BrentSeidel/Arduino-Sensor-Network/Schematics/Basic Responder.kicad_sch

## KiCad design Schematics/Basic Responder.kicad_sch (2023-06-15)

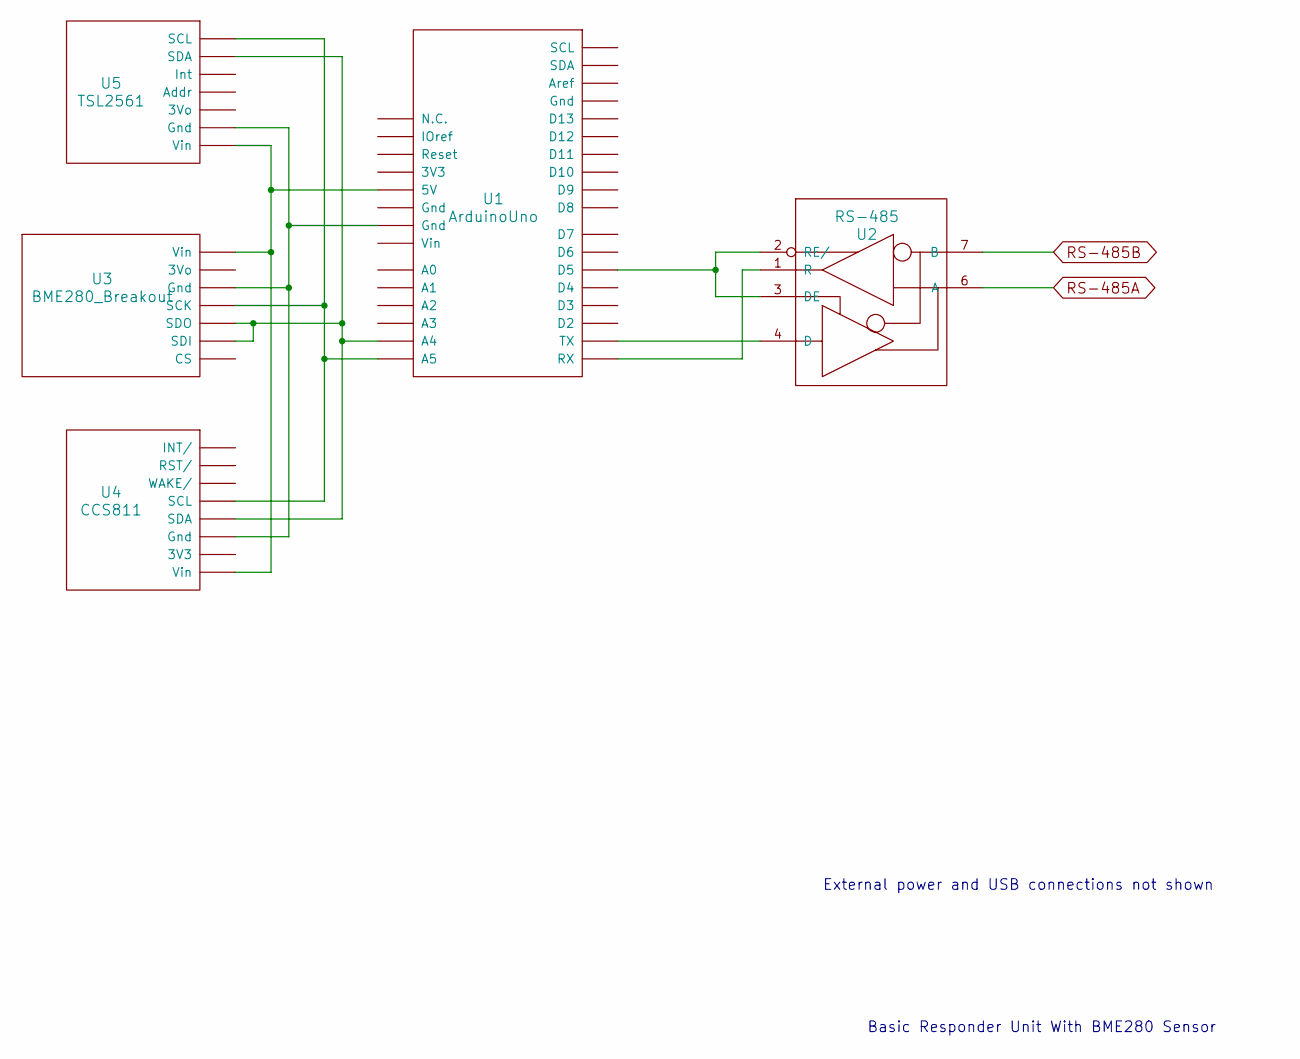
[picture p12: schematic Basic Responder.kicad_sch]

Parts:
U1: ArduinoUno
U2: RS-485
U3: BME280_Breakout
U4: CCS811
U5: TSL2561

Connections:
unnamed: U1.~, U2.1 (R), U2.2 (RE/), U2.3 (DE), U2.4 (D), U3.~, U4.~, U5.~
RS-485A: U2.6 (A)
RS-485B: U2.7 (B)

Notes on the sheet:
External power and USB connections not shown
Basic Responder Unit With BME280 Sensor
