BrentSeidel/Arduino-Sensor-Network/Schematics/Controller.kicad_sch

## KiCad design Schematics/Controller.kicad_sch (2023-06-15)

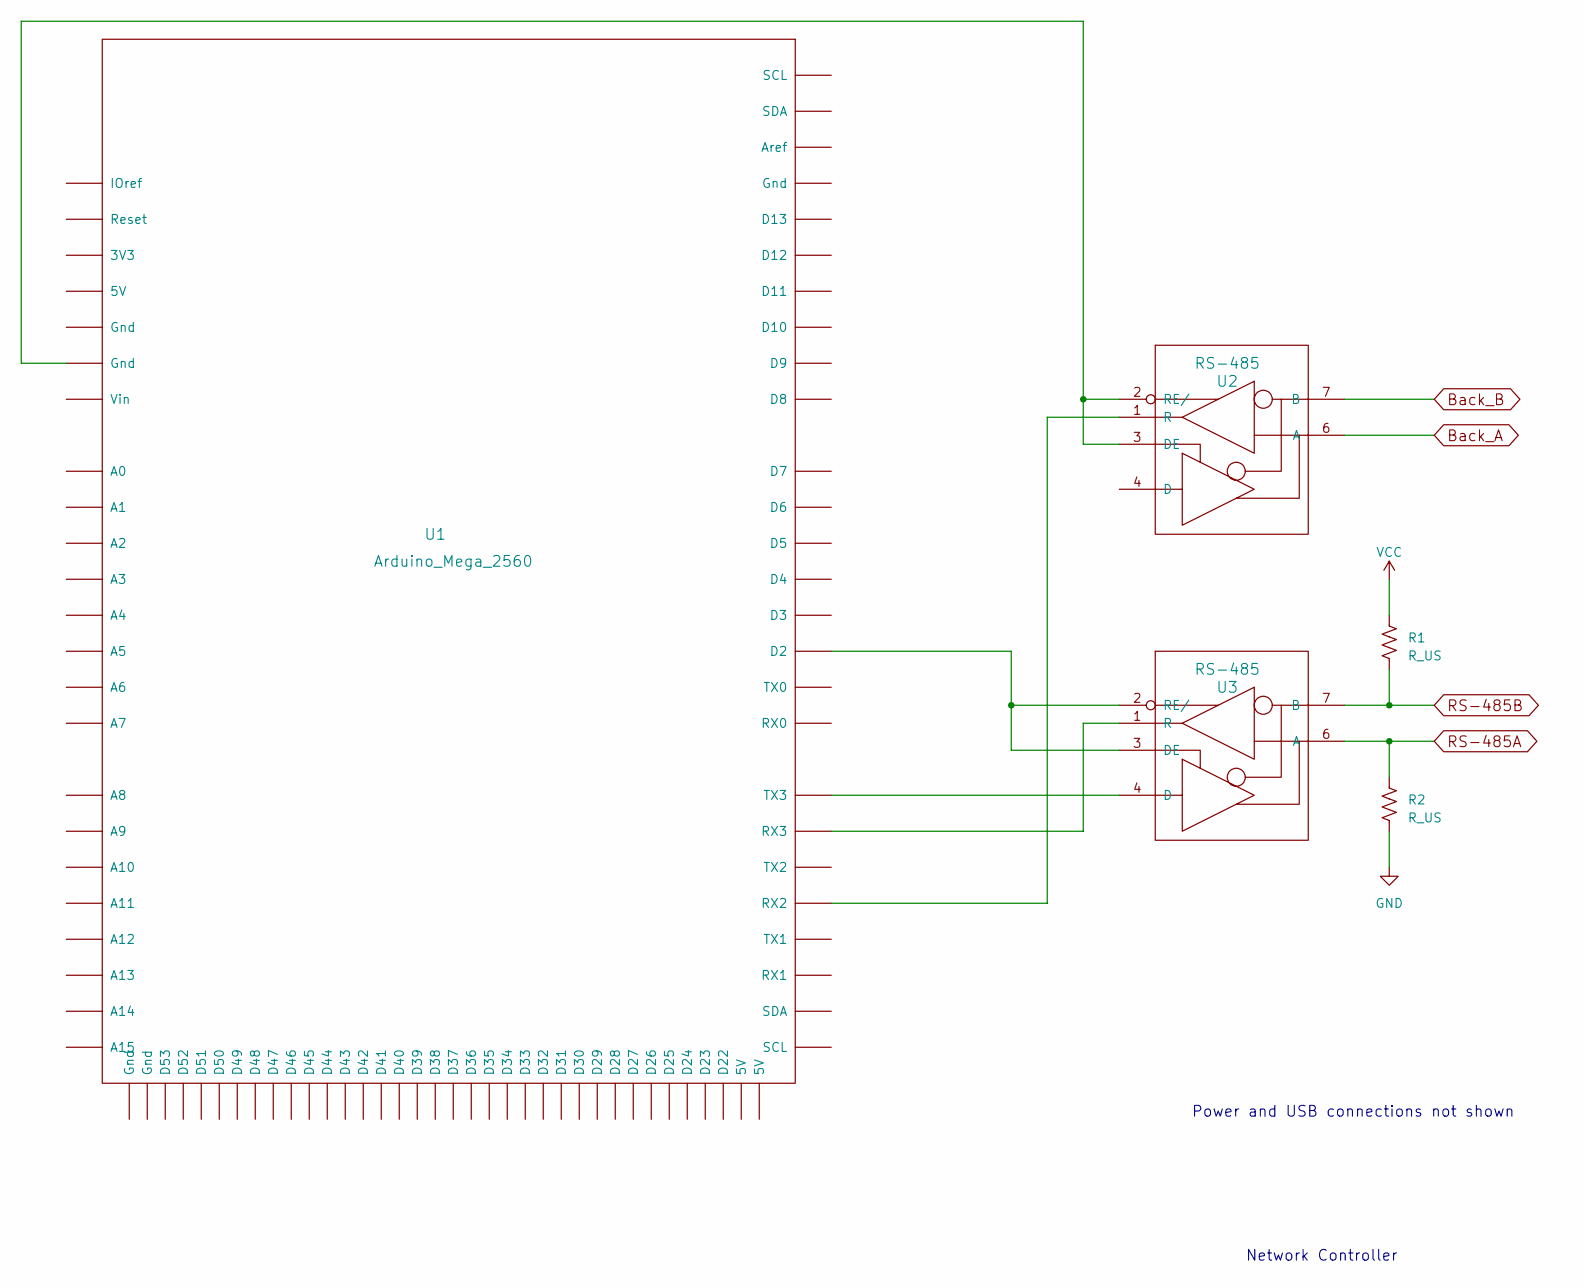
[picture p13: schematic Controller.kicad_sch]

Parts:
R1, R2: R_US
U1: Arduino_Mega_2560
U2, U3: RS-485

Connections:
Back_A: U2.6 (A)
Back_B: U2.7 (B)
GND: R2.2
unnamed: U1.~, U2.1 (R), U2.2 (RE/), U2.3 (DE), U3.1 (R), U3.2 (RE/), U3.3 (DE), U3.4 (D)
RS-485A: R2.1, U3.6 (A)
RS-485B: R1.2, U3.7 (B)
VCC: R1.1

Notes on the sheet:
Power and USB connections not shown
Network Controller
