BrentSeidel/Arduino-Sensor-Network/Schematics/Web Gateway.kicad_sch

## KiCad design Schematics/Web Gateway.kicad_sch (2023-06-15)

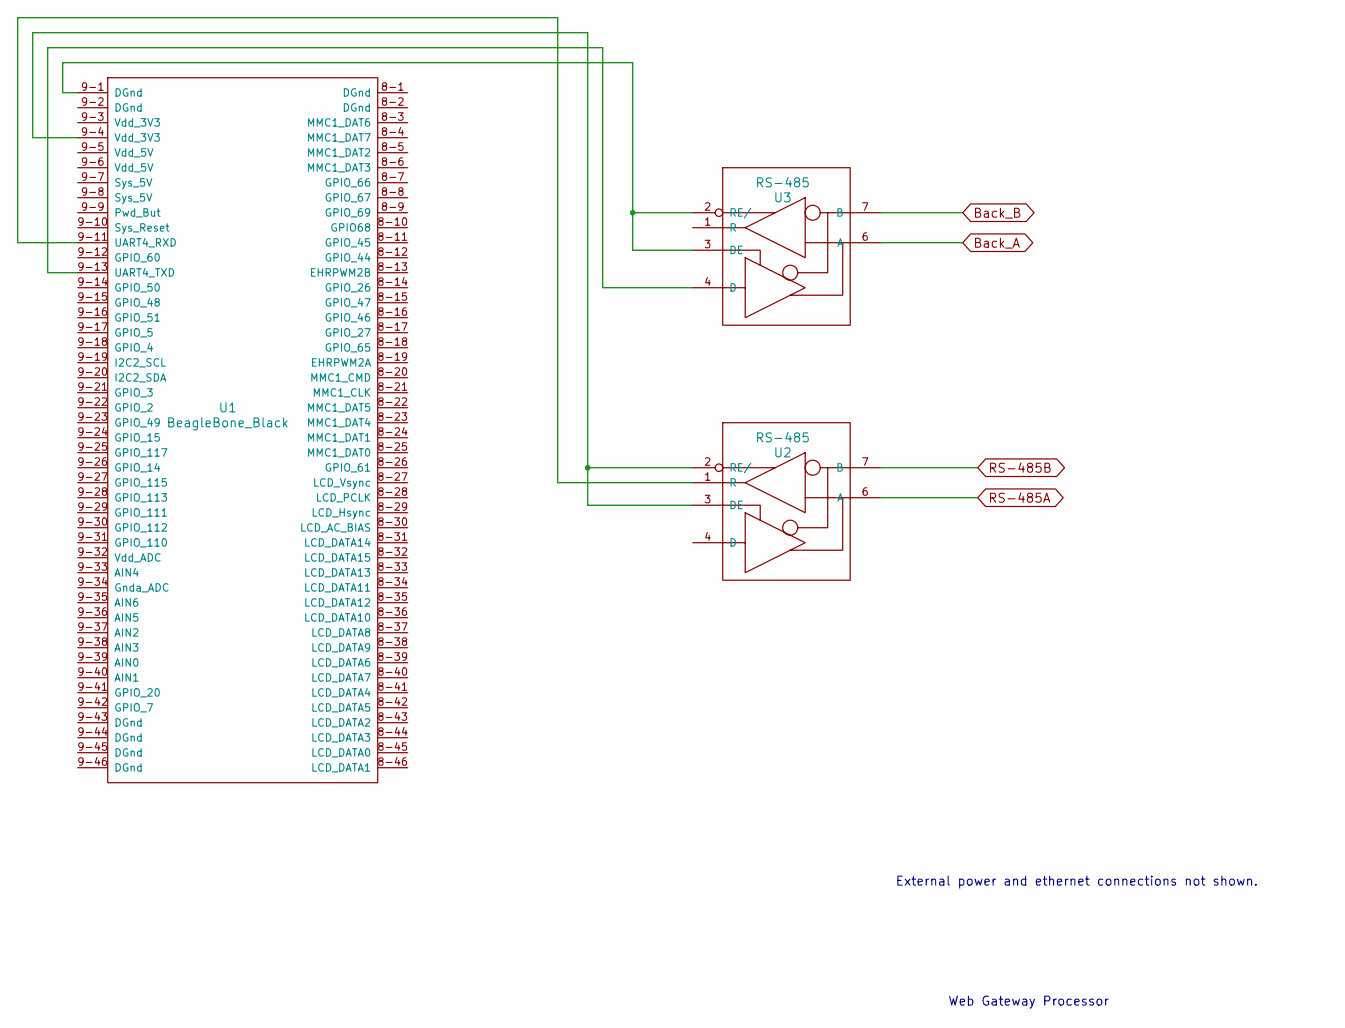
[picture p14: schematic Web Gateway.kicad_sch]

Parts:
U1: BeagleBone_Black
U2, U3: RS-485

Connections:
Back_A: U3.6 (A)
Back_B: U3.7 (B)
unnamed: U1.9-1 (DGnd), U3.2 (RE/), U3.3 (DE)
unnamed: U1.9-4 (Vdd_3V3), U2.2 (RE/), U2.3 (DE)
unnamed: U1.9-11 (UART4_RXD), U2.1 (R)
unnamed: U1.9-13 (UART4_TXD), U3.4 (D)
RS-485A: U2.6 (A)
RS-485B: U2.7 (B)

Notes on the sheet:
External power and ethernet connections not shown.
Web Gateway Processor
