BrentSeidel/Arduino-Sensor-Network/Schematics/rescue-backup/Basic Responder-2023-06-14-08-46-27.sch

## KiCad design Schematics/rescue-backup/Basic Responder-2023-06-14-08-46-27.sch (2018-10-10)

Schematic: Basic Responder-2023-06-14-08-46-27.sch

Parts:
U1: ArduinoUno
U2: RS-485
U3: BME280_Breakout

Notes on the sheet:
Basic Responder Unit With BME280 Sensor
External power and USB connections not shown
