BrentSeidel/Arduino-Sensor-Network/Schematics/rescue-backup/Controller-2023-06-14-08-46-27.sch

## KiCad design Schematics/rescue-backup/Controller-2023-06-14-08-46-27.sch (2018-10-10)

Schematic: Controller-2023-06-14-08-46-27.sch

Parts:
U1: Arduino_Mega_2560
U2, U3: RS-485

Notes on the sheet:
Network Controller
Power and USB connections not shown
